CircuitGuy943/The-Klipper-Console-V1/Pictures/IMG_20260112_180502.jpg

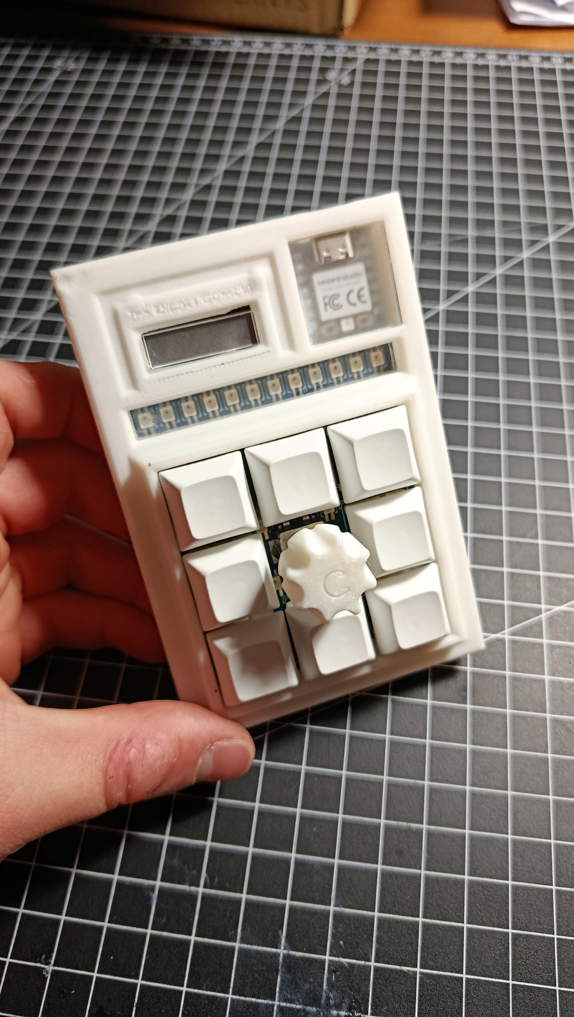
Pictures/IMG_20260112_180502.jpg
