CircuitGuy943/The-Klipper-Console-V1/Pictures/PCB3DView.png

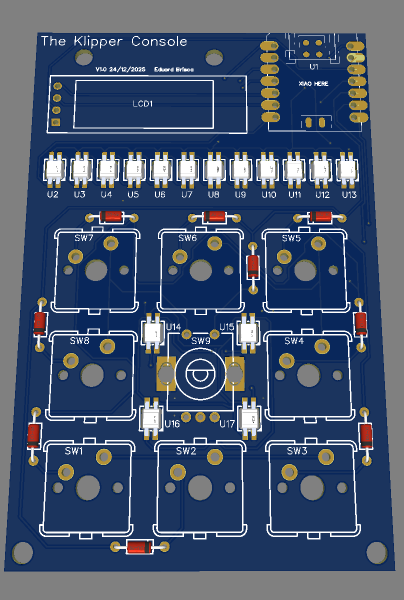
Pictures/PCB3DView.png
